jharvey/MultiMAP/multi_map_kicad/SIM/diodes_1.PNG

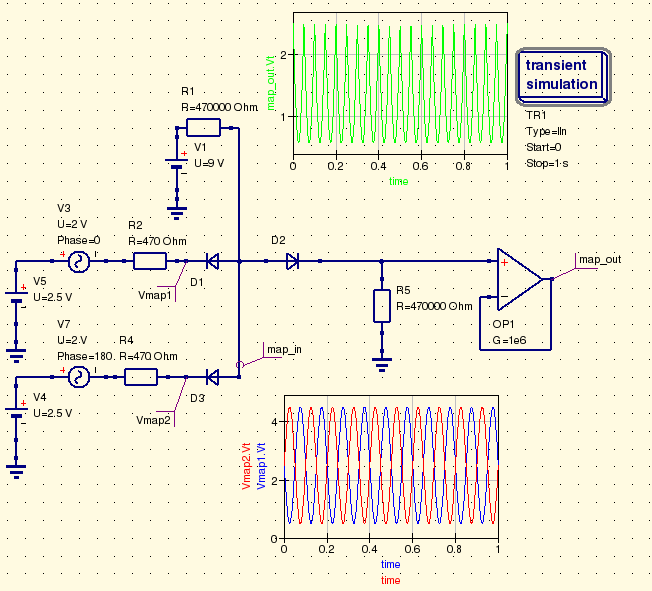
multi_map_kicad/SIM/diodes_1.PNG
