jharvey/MultiMAP/pictures/2010-04-24 004.JPG

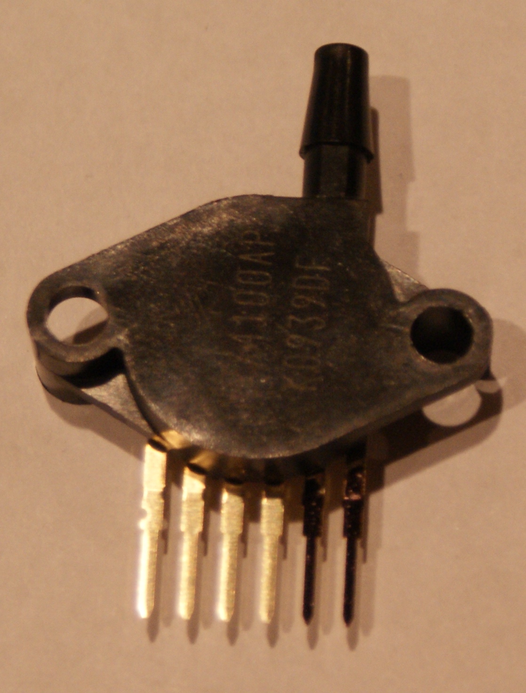
pictures/2010-04-24 004.JPG
