jharvey/MultiMAP/pictures/2010-04-24 005.JPG

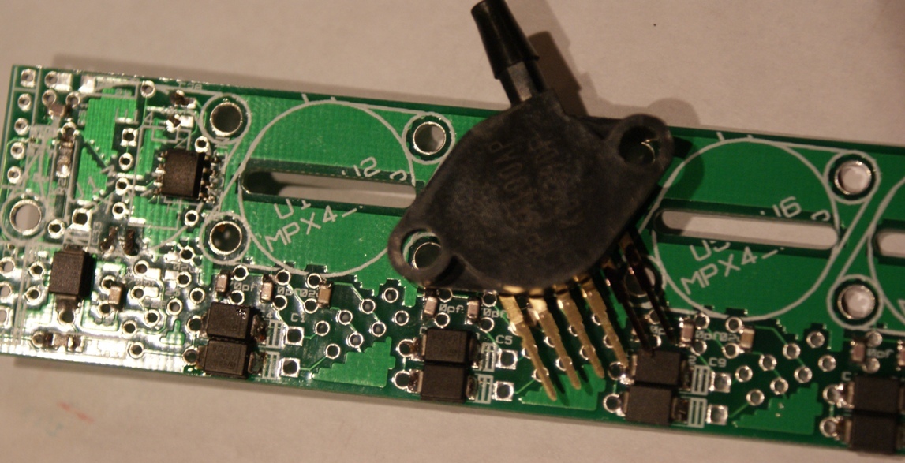
pictures/2010-04-24 005.JPG
