jharvey/MultiMAP/pictures/2010-05-29 003.JPG

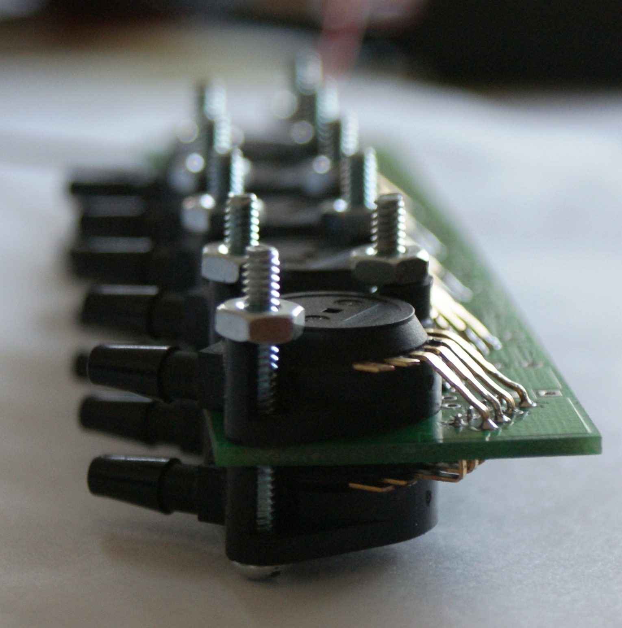
pictures/2010-05-29 003.JPG
