jharvey/MultiMAP/pictures/2010-05-29 004.JPG

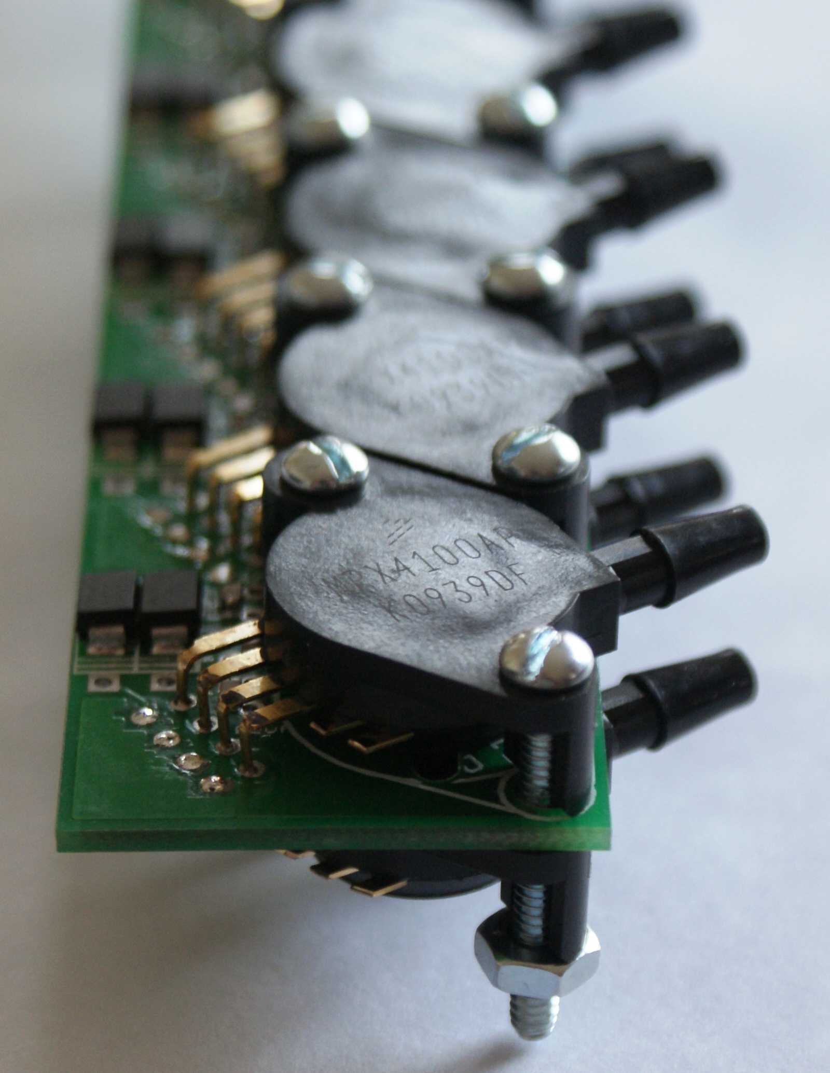
pictures/2010-05-29 004.JPG
