jharvey/MultiMAP/pictures/other/2010-04-24 002.JPG

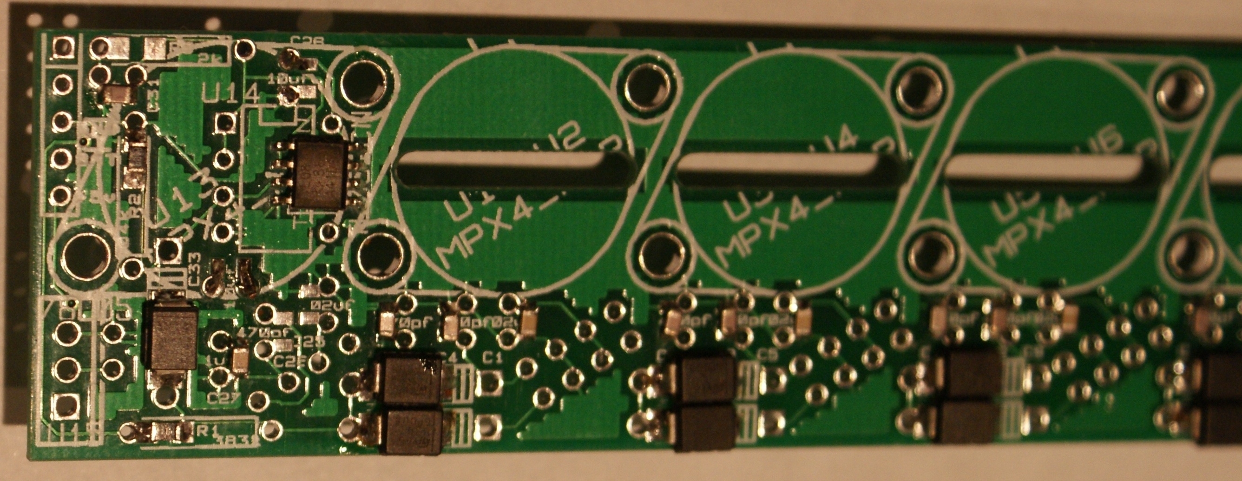
pictures/other/2010-04-24 002.JPG
