jharvey/MultiMAP/pictures/other/2010-04-24 003.JPG

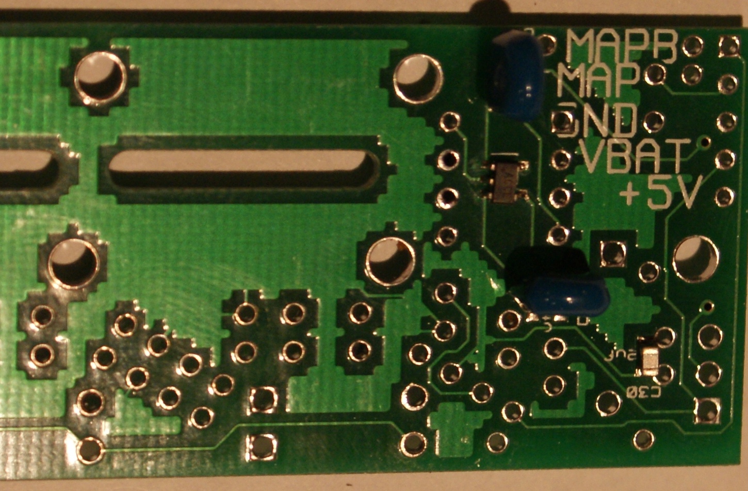
pictures/other/2010-04-24 003.JPG
