jharvey/MultiMAP/pictures/other/2010-05-28 004.JPG

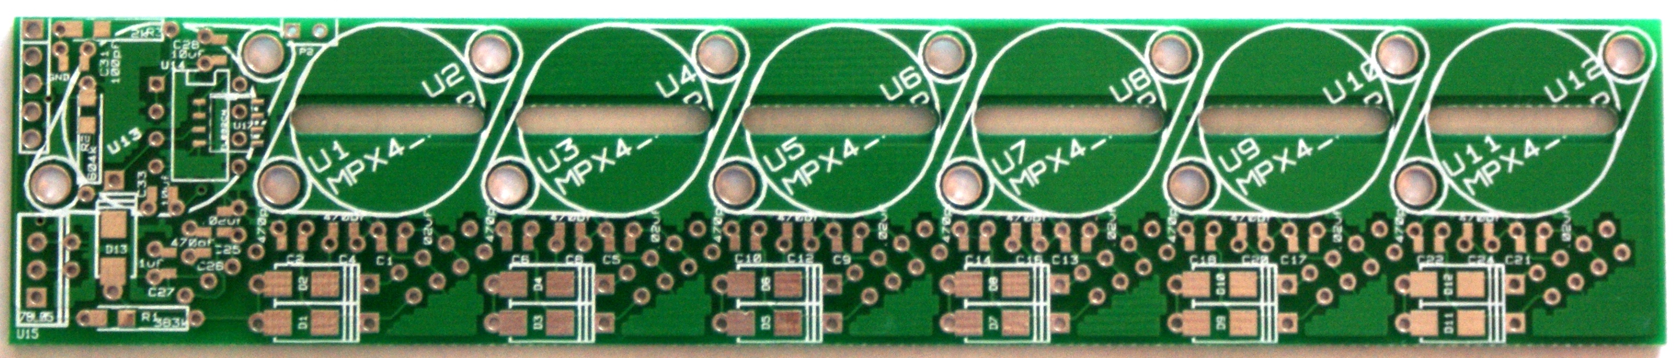
pictures/other/2010-05-28 004.JPG
