jharvey/MultiMAP/pictures/other/2010-05-28 005.JPG

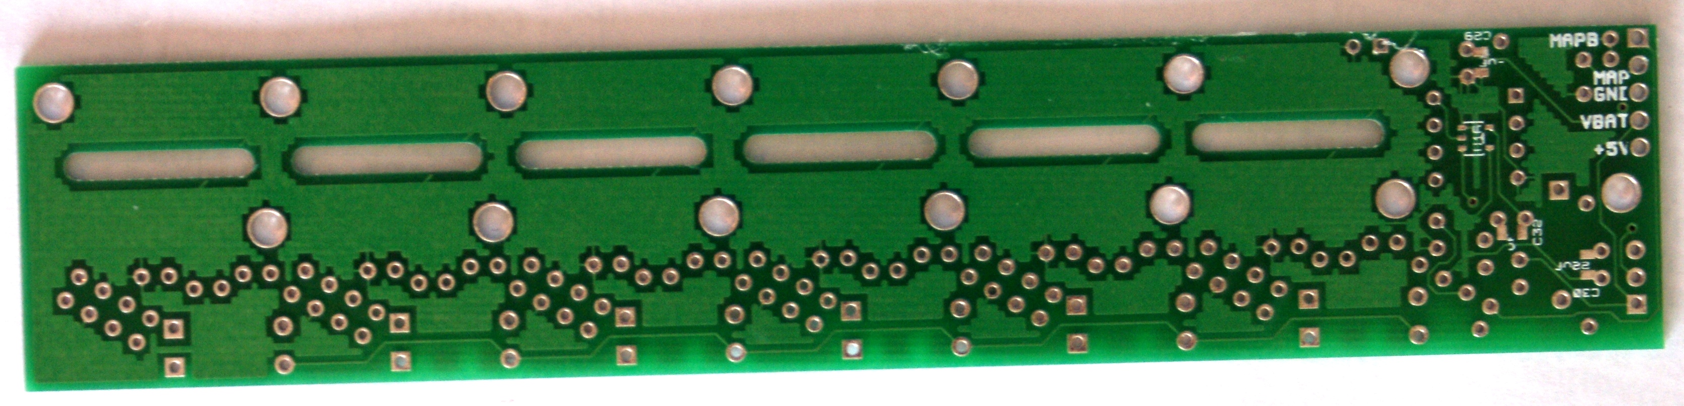
pictures/other/2010-05-28 005.JPG
