jharvey/MultiMAP/old/multi_map-MaskCmp.pdf

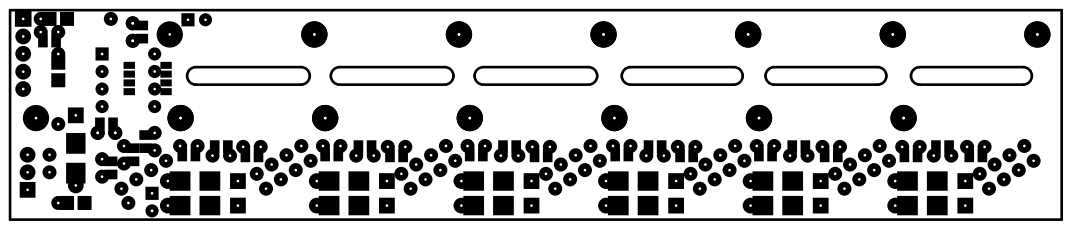
[picture p71: page 1]
