jharvey/MultiMAP/old/multi_map-MaskCopp.pdf

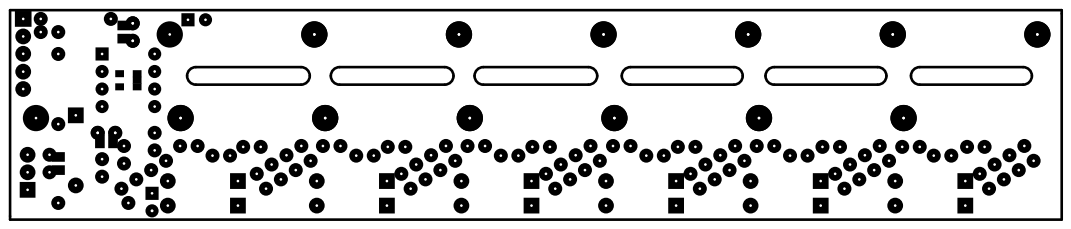
[picture p72: page 1]
