jharvey/MultiMAP/old/multi_map-SilkSCmp.pdf

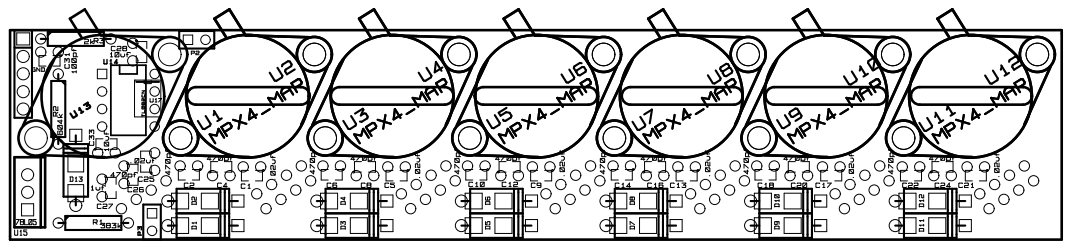
[picture p73: page 1]
