jharvey/MultiMAP/old/multi_map-SilkSCop-mirrored.pdf

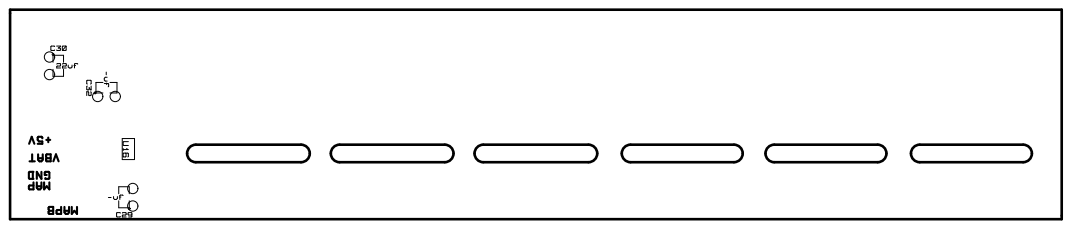
[picture p74: page 1]
