jharvey/MultiMAP/old/multi_map-SilkSCop.pdf

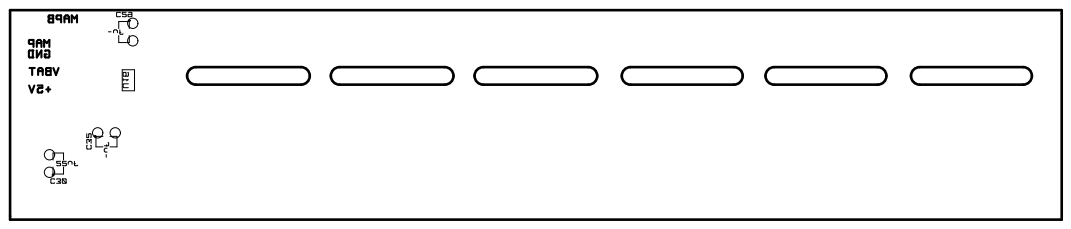
[picture p75: page 1]
