jharvey/MultiMAP/old/multi_map-SoldPCmp.pdf

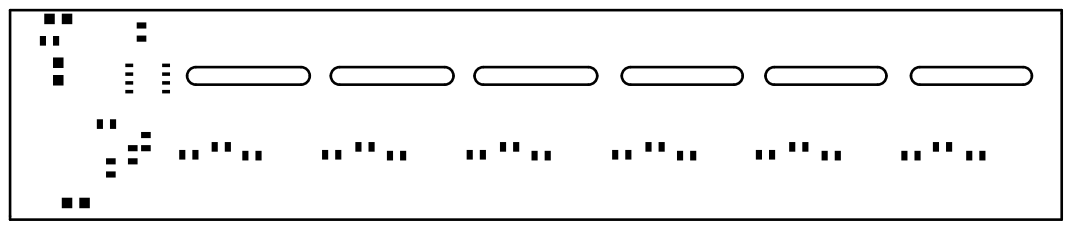
[picture p76: page 1]
