jharvey/MultiMAP/old/multi_map-SoldPCop.pdf

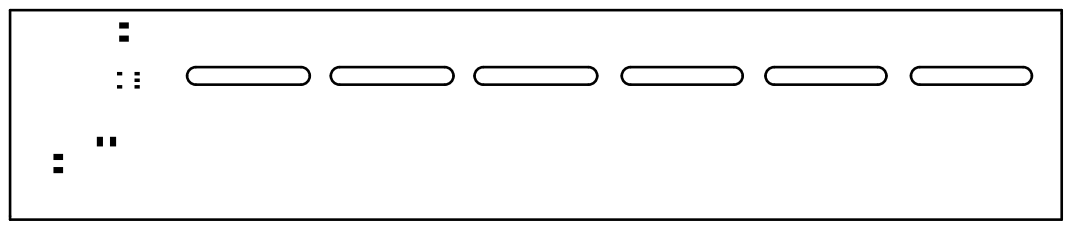
[picture p77: page 1]
