jharvey/MultiMAP/old/multi_map.pdf

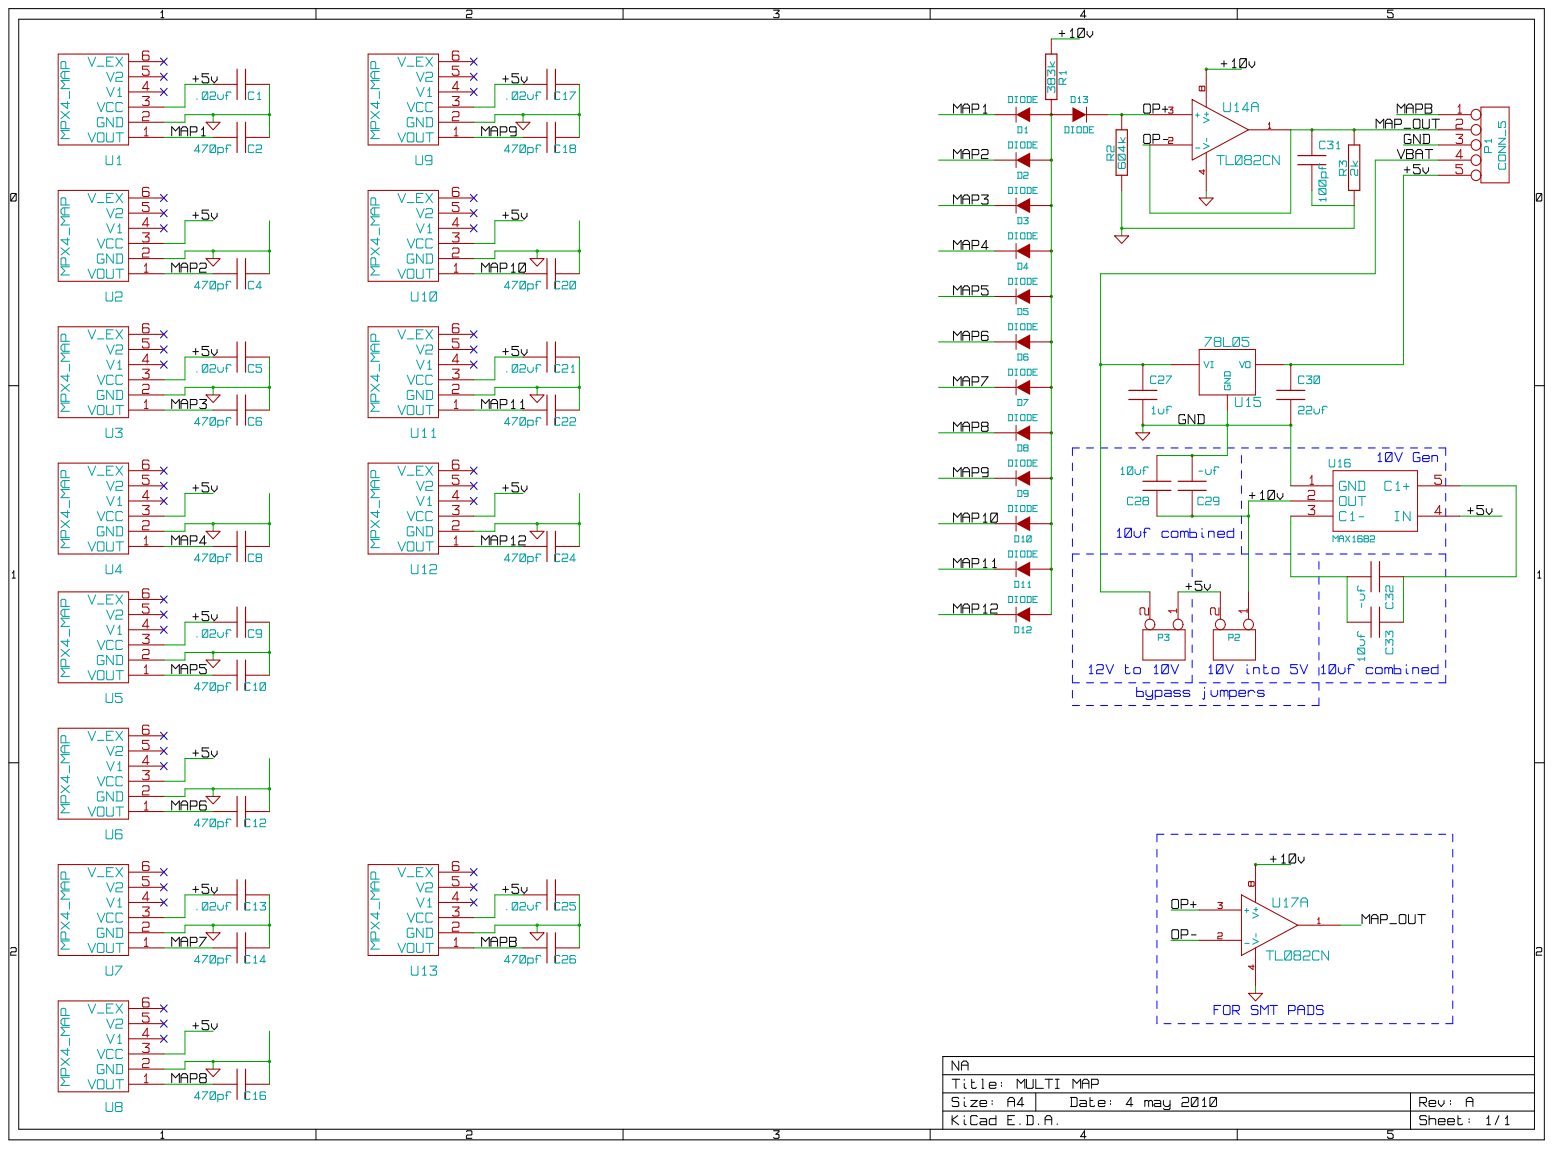
[picture p78: page 1]
