jharvey/MultiMAP/multi_map_kicad/multi_map.sch

## KiCad design multi_map_kicad/multi_map.sch (2020-05-19, an earlier design)

Schematic: multi_map.sch

Parts:
C1, C5, C9, C13, C17, C21, C25: .02uf; SM0805-C1
C2, C4, C6, C8, C10, C12, C14, C16, C18, C20, C22, C24, C26: 470pf; SM0805-C1
C27: 1uf; SM0805-C1
C28, C33: 10uf; SM0805-C1
C29, C32: -uf; SM0805-C1
C30: 22uf; SM0805-C1
C31: 100pf; SM0805-C1
D1, D2, D3, D4, D5, D6, D7, D8, D9, D10, D11, D12, D13: DIODE; D4-SMB
P1: CONN_5; SIL-5
P2, P3: CONN_2; sil-2
R1: 383k; R4-SM0805
R2: 604k; R4-SM0805
R3: 2k; R4-SM0805
U1, U3, U5, U7, U9, U11, U13: MPX4_MAP; MPX-4_MAP_2
U2, U4, U6, U8, U10, U12: MPX4_MAP; MPX-4_MAP
U14: TL082CN; 8DIP300
U15: 78L05; TO220_VERT
U16: MAX1682; SOT23-5
U17: TL082CN; SO8E

Notes on the sheet:
10V Gen
12V to 10V
bypass jumpers
10V into 5V
FOR SMT PADS
10uf combined
